ethylowy/Ender-3_v3_SE-KE_Mod/Configuration/end.cfg

[gcode_macro PRINT_END]
gcode:
  G91  ;Set to relative positioning
  G0 Z10 F3000  ;Move Up
  G90  ;Set to absolute positioning
  G0 X0 Y220 F7500  ;Move XY
  TURN_OFF_HEATERS  ;Turn off heaters
  M84  ;Disable motors
  M106 S0  ;Part cooling fan speed
  BED_MESH_PROFILE REMOVE=automatic
  SET_PRESSURE_ADVANCE ADVANCE=0.0
  SET_IDLE_TIMEOUT TIMEOUT=600
