ethylowy/Ender-3_v3_SE-KE_Mod/Configuration/macros.cfg

[gcode_macro _CLIENT_VARIABLE]
gcode:
  variable_use_fw_retract   : True

[gcode_macro PID_EXTRUDER]
gcode:
 M106 S255
 {% set TARGET_TEMP = params.TARGET_TEMP|default(210)|float %} 
 PID_CALIBRATE HEATER=extruder TARGET={TARGET_TEMP}
 SAVE_CONFIG

[gcode_macro PID_BED]
gcode:
 {%set TARGET_TEMP = params.TARGET_TEMP|default(70)|float %}
 PID_CALIBRATE HEATER=heater_bed TARGET={TARGET_TEMP}
 SAVE_CONFIG

[gcode_macro BEEP]
gcode:
    {% set duration = params.P|default(100)|float %}
    SET_PIN PIN=beeper VALUE=1
    G4 P{duration}
    SET_PIN PIN=beeper VALUE=0

[gcode_macro MOVE_TO_NEUTRAL_POSITION]
gcode:
  g28; home all axis
  g90; set to absolute positioning
  g1 x110 y110 f9000
  g1 z100 f3000
  M83; set extruder to relative positioning

[gcode_macro SURFACE_MAP]
gcode:
  g28; home all axis
  BED_MESH_CALIBRATE METHOD=automatic

[gcode_macro Z_OFFSET]
gcode:
  g28; home all axis
  PROBE_CALIBRATE

[gcode_macro Z_CHECK]
gcode:
  g28; home all axis
  PROBE_ACCURACY

[gcode_macro INPUTSHAPER_X]
gcode:
  M84
  G90
  G28
  SHAPER_CALIBRATE AXIS=x
  SAVE_CONFIG

[gcode_macro INPUTSHAPER_Y]
gcode:
  M84
  G90
  G28
  SHAPER_CALIBRATE AXIS=y
  SAVE_CONFIG

[gcode_macro Direct_PA_Tunning]
gcode:
  SET_VELOCITY_LIMIT SQUARE_CORNER_VELOCITY=1 ACCEL=500
  TUNING_TOWER COMMAND=SET_PRESSURE_ADVANCE PARAMETER=ADVANCE START=0 FACTOR=.005

[gcode_macro Bowden_PA_Tunning]
gcode:
  SET_VELOCITY_LIMIT SQUARE_CORNER_VELOCITY=1 ACCEL=500
  TUNING_TOWER COMMAND=SET_PRESSURE_ADVANCE PARAMETER=ADVANCE START=0 FACTOR=.020
