ethylowy/Ender-3_v3_SE-KE_Mod/Configuration/start.cfg

[gcode_macro PRINT_START]
gcode:
  {% set BED_TEMP = params.BED_TEMP|default(80)|float %}
  {% set EXTRUDER_TEMP = params.EXTRUDER_TEMP|default(220)|float %}
    SET_PRESSURE_ADVANCE ADVANCE=0.0
    SET_IDLE_TIMEOUT TIMEOUT=43200
    G28  ;Home all Axes
    BED_MESH_CALIBRATE PROFILE=automatic METHOD=automatic probe_count=5,5 mesh_min=25,25 mesh_max=195,195 ADAPTIVE=1 ADAPTIVE_MARGIN=5 ; Auto-generate mesh around print area
    G28  ;Home all Axes
    M140 S{BED_TEMP}; Start bed heating
    M109 S{EXTRUDER_TEMP}; Set and wait for nozzle to reach temperature
    M190 S{BED_TEMP}; Wait for bed to reach temperature
    M83; set extruder to relative positioning
	G1 Z1.0 F1500; move z up little to prevent scratching the bed			
	G1 X50.0 Y0.2 Z0.3 F1500.0; move to start-line position	
	G1 X150.0 Y0.2 Z0.3 F750.0 E10; draw 1st line
	G1 X150.0 Y0.6 Z0.3 F1500.0; move to side a little	
	G1 X50.0 Y0.6 Z0.3 F750.0 E20; draw 2nd line
	G1 Z1.0 F1500; move z up little to prevent scratching the bed
    G28  ;Home all Axes
