ethylowy/Ender-3_v3_SE-KE_Mod/Configuration/adxl.cfg

[mcu adxl]
serial: /dev/serial/by-id/usb-Klipper_rp2040_E66118C4172CB926-if00

[adxl345]
cs_pin: adxl:gpio1
spi_bus: spi0a
axes_map: x,z,y

[resonance_tester]
accel_chip: adxl345
probe_points:
    117.5,117.5,10

[output_pin power_mode] # Improve power stability
pin: adxl:gpio23

[gcode_macro INPUTSHAPER_X]
gcode:
  M84
  G90
  G28
  SHAPER_CALIBRATE AXIS=x
  SAVE_CONFIG 

[gcode_macro INPUTSHAPER_Y]
gcode:
  M84
  G90
  G28
  SHAPER_CALIBRATE AXIS=y
  SAVE_CONFIG 
